holmesrichards/arpenvfol/Simulations/arpenvfol.asc

B1: bv; V=V(input)*V(envin)/8
C1: cap; 20p
C2: cap; 20p
C3: cap; 20p
C4: cap; 1µ
C5: cap; 100n
C6: cap; 10n
C7: cap; 2n
C8: cap; 1n
C9: cap; 1n
C10: cap; {c14}
C11: cap; 1n
C12: cap; {c14}
C13: cap; 1n
C14: cap; {c14}
C15: cap; 100n
D1: diode
D2: diode
D3: diode; 1N4148
D4: diode; 1N4148
D5: diode; 1N4148
D6: diode; 1N4148
D7: diode; 1N4148
D8: diode; 1N4148
D9: diode; 1N4148
D10: diode; 1N4148
D11: diode; 1N4148
D12: diode; 1N4148
D13: diode; 1N4148
D14: diode; 1N4148
D15: diode; 1N4148
M1: nmos; VN2222LL
M2: nmos; VN2222LL
M3: nmos; VN2222LL
R1: res; 82k
R2: res; 39k
R3: res; 100k
R4: res; 100k
R5: res; 100k
R6: res; 120k
R7: res; 100k
R8: res; 100k
R9: res; 2.7k
R10: res; 27k
R11: res; 270k
R12: res; 1Meg
R13: res; 3Meg
R14: res; 1.5Meg
R15: res; 10k
R16: res; 100k
R17: res; 10k
R18: res; 10k
R19: res; 100k
R20: res; 10k
R21: res; 1k
R22: res; 100k
R23: res; 10k
R24: res; 1k
R25: res; 100
R26: res; 100k
U1: TL074
U2: potentiometer; Rtot=100K wiper={wp}
U3: TL074
U4: TL074
U5: TL074
U6: TL074
U7: TL074
U8: TL074
U9: TL074
U10: TL074
U11: TL074
U13: TL074
U14: TL074
U15: TL074
V1: voltage; 12
V2: voltage; -12
V3: voltage; SINE(0 8 {fr} 0 0 0); AC 5 0
V4: voltage; PWL(0 .001 {r} 8 400m 6 {f} 6 800m 0 1000m 0); AC 5 0
V5: voltage; PULSE(0 12 0 .001u .001u .01 .02)
V6: voltage; PULSE(0 12 0.00667 .001u .001u .01 .02)
V7: voltage; PULSE(0 12 0.01333 .001u .001u .01 .02)
Named nets: 0, Vp12, Vm12, INPUT, ENVIN, INWITHENV, ENVOUT, OUTBIS1, CLOCK1, OUTBIS2, CLOCK2, OUTBIS3, CLOCK3, OUTBIS
;op
.param wp=.56
.tran 0 1 0
;.step param wp 0 1 .25
;.step param fr list 83 123 166 206 249
.param fr=103
.model BS170 VDMOS VTO=1.824 RG=270 RS=1.572 RD=1.436 RB=.768 KP=.1233 Cgdmax=20p Cgdmin=3p CGS=28p Cjo=35p Rds=1.2E8 IS=5p Bv=60 Ibv=10u Tt=161.6n
.MODEL VN2222LL NMOS (LEVEL=3 RS=0.205 NSUB=1.0E15 KAPPA=0.0506 TPG=1 CGDO=3.1716n RD=0.439 VTO=1.6 VMAX=1.0E7 ETA=0.0223089 NFS=6.6E10 TOX=1.0E-7 LD=1.698n UO=862.425 XJ=6.4666E-7 THETA=1.0E-5 CGSO=9.09n L=2.5E-6 W=0.8E-2)
;.step param c14 list 1n 2n 5n 10n
.param c14=20n
.step param r list 0.001m 20m 50m 100m 200m 300m
.param f=800m-{r}
